janbert/VSTiBox/sw/host .NET/VSTiBox/Resources/powerbutton.png

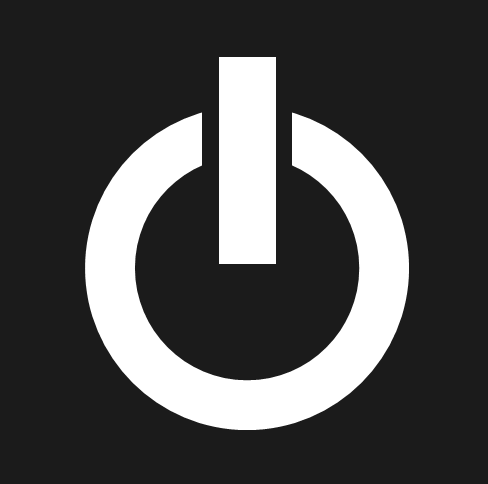
sw/host .NET/VSTiBox/Resources/powerbutton.png
