janbert/VSTiBox/sw/control/driver/rom_drivers.h

/****************************************************************************
 *   $Id:: rom_drivers.h 41 2012-02-12 16:03:02Z sander                 $
 *   Project: NXP LPC11xx CAN example
 *
 *   Description:
 *     This file is part of the CAN and CANopen on-chip driver examples.
 *
 ****************************************************************************
 * Software that is described herein is for illustrative purposes only
 * which provides customers with programming information regarding the
 * products. This software is supplied "AS IS" without any warranties.
 * NXP Semiconductors assumes no responsibility or liability for the
 * use of the software, conveys no license or title under any patent,
 * copyright, or mask work right to the product. NXP Semiconductors
 * reserves the right to make changes in the software without
 * notification. NXP Semiconductors also make no representation or
 * warranty that such application will be suitable for the specified
 * use without further testing or modification.
****************************************************************************/
#ifndef ROM_DRIVERS_H_
#define ROM_DRIVERS_H_

#if CONFIG_ENABLE_DRIVER_ROMCAN==1
	#include "rom_driver_CAN.h"
#endif /* (PERIPHERAL == CAN) */

#if CONFIG_ENABLE_DRIVER_ROMUSB==1
	#include "usb.h" 
	typedef	struct _USB {
	  void (*init_clk_pins)(void);
	  void (*isr)(void);
	  void (*init)( USB_DEV_INFO * DevInfoPtr ); 
	  void (*connect)(BOOL  con);
	}USB;
#endif /* (PERIPHERAL == USB) */

#if CONFIG_ENABLE_DRIVER_ROMPOWER==1
typedef	struct _PWRD {
  void (*set_pll)(unsigned int cmd[], unsigned int resp[]);
  void (*set_power)(unsigned int cmd[], unsigned int resp[]);
}  PWRD;

//PLL setup related definitions
#define	CPU_FREQ_EQU  		0       //main PLL freq must be equal to the specified 
#define	CPU_FREQ_LTE		1       //main PLL freq must be less than or equal the specified
#define	CPU_FREQ_GTE		2       //main PLL freq must be greater than or equal the specified
#define	CPU_FREQ_CLOSE		3       //main PLL freq must be as close as possible the specified

#define	PLL_CMD_CUCCESS		0       //PLL setup successfully found
#define	PLL_INVALID_FREQ	1       //specified freq out of range (either input or output)
#define	PLL_INVALID_MODE	2       //invalid mode (see above for valid) specified
#define	PLL_FREQ_NOT_FOUND	3       //specified freq not found under specified conditions
#define	PLL_NOT_LOCKED		4       //PLL not locked => no changes to the PLL setup

//power setup elated definitions
#define	PARAM_DEFAULT			0   //default power settings (voltage regulator, flash interface)
#define	PARAM_CPU_EXEC			1   //setup for maximum CPU performance (higher current, more computation)
#define	PARAM_EFFICIENCY		2   //balanced setting (power vs CPU performance)
#define	PARAM_LOW_CURRENT		3   //lowest active current, lowest CPU performance

#define	PARAM_CMD_CUCCESS		0   //power setting successfully found
#define	PARAM_INVALID_FREQ		1   //specified freq out of range (=0 or > 50 MHz)
#define	PARAM_INVALID_MODE		2   //specified mode not valid (see above for valid)

#define MAX_CLOCK_KHZ_PARAM                50000

#endif

#if CONFIG_ENABLE_DRIVER_ROMCAN==1 || \
	CONFIG_ENABLE_DRIVER_ROMUSB==1 || \
	CONFIG_ENABLE_DRIVER_ROMPOWER==1
typedef	struct _ROM {
   const unsigned p_usbd;
   const unsigned p_clib;
#if CONFIG_ENABLE_DRIVER_ROMCAN==1
   const CAND *pCAND;
#else
   const unsigned pCAND;
#endif /* (PERIPHERAL == CAN) */
#if CONFIG_ENABLE_DRIVER_ROMPOWER==1
   const PWRD * pPWRD;
#else
   const unsigned p_pwrd;
#endif /* PWRROMD_PRESENT */
   const unsigned p_dev1;
   const unsigned p_dev2;
   const unsigned p_dev3;
   const unsigned p_dev4; 
}  ROM;
#endif

#endif /* ROM_DRIVERS_H_ */
